SirBramble/The-Macruwu/Macruwu_OS/Mapping.cpp

#include "Mapping.h"
#include "Keyboard.h"


Keyboard Keyboard1;

void keyboardSetup(){
  Keyboard1.init();
}

void button1(){
  Keyboard1.write("$$");
  Keyboard1.goLeft(1);
	Serial.println("Button1");
}

void button2(){
	Keyboard1.backslash();
  Keyboard1.write("infty");
  Serial.println("Button2");
}

void button3(){
  Keyboard1.backslash();
	Keyboard1.write("sqrt");
  Keyboard1.brackets(1);
	Serial.println("Button3");
}

void button4(){
	Keyboard1.writeKeycode(56, KEYBOARD_MODIFIER_LEFTSHIFT);
  Keyboard1.brackets(1);
	Serial.println("Button4");
}

void button5(){
	Keyboard1.backslash();
  Keyboard1.write("underline");
  Keyboard1.brackets(1);
	Serial.println("Button5");
}

void button6(){
	Keyboard1.writeKeycode(HID_KEY_GRAVE);
  Keyboard1.brackets(1);
	Serial.println("Button6");
}

void button7(){
	Keyboard1.write("e");
	Serial.println("Button7");
}

void button8(){
	Keyboard1.backslash();
	Keyboard1.write("frac");
  Keyboard1.brackets(0);
  Keyboard1.brackets(0);
  Keyboard1.goLeft(3);
	Serial.println("Button8");
}

void button9(){
	
	Serial.println("Button9");
}

void button10(){
	
	Serial.println("Button10");
}

void button11(){
	
	Serial.println("Button11");
}

void button12(){
	Keyboard1.backslash();
  Keyboard1.write("left");
  Keyboard1.writeKeycode(0x64, KEY_MOD_RALT);
  Keyboard1.backslash();
  Keyboard1.write("right");
  Keyboard1.writeKeycode(0x64, KEY_MOD_RALT);
  Keyboard1.goLeft(7);
	Serial.println("Button12");
}

void button13(){
  Keyboard1.backslash();
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

		case 25:
			button25();
		break;

		case 26:
			button26();
		break;

		case 27:
			button27();
		break;

		case 28:
			button28();
		break;

		case 29:
			button29();
		break;

		case 30:
			button30();
		break;

		case 31:
			button31();
		break;

		case 32:
			button32();
		break;

	}
}
